william-redenbaugh/lazy-board/Housing files/Housing working/dxf 2000/Layer5.dxf

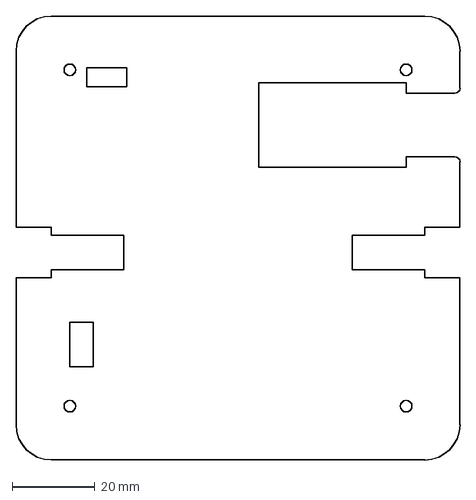
[picture p7: CAD file, 2019-08-05]
Housing files/Housing working/dxf 2000/Layer5.dxf
107.3 x 107.3 mm
