william-redenbaugh/lazy-board/lazy-code/Teensy4LazyBoard/src/led_matrix_handler.cpp

/*
Author: William Redenbaugh
Last Edit Date: 7/3/2020
*/

#include "led_matrix_handler.hpp"

// SERIAL DMA FOR LED MATRIX BEGIN // 

// default number of matrix_leds. 
const int num_matrix_led = NUM_MATRIX_LEDS;
// Default GPIO value. 
uint8_t led_matrix_gpio = LED_MATRIX_GPIO;

byte matrix_drawing_memory[num_matrix_led*3];         //  3 bytes per LED for RGB
DMAMEM byte matrix_display_memory[num_matrix_led*12]; // 12 bytes per LED for RGB

WS2812Serial matrix_leds = WS2812Serial(num_matrix_led, matrix_display_memory, matrix_drawing_memory, led_matrix_gpio, WS2812_GRB);

// SERIAL DMA FOR LED MATRIX END // 

// SERIAL DMA FOR LED UNDERGLOW BEGIN //

// Default GPIO value. 
const int num_underglow_led = UNDERGLOW_NUM_LEDS;
uint8_t led_underglow_gpio = UNDERGLOW_STRIP_GPIO;

byte underglow_drawing_memory[num_underglow_led*3];         //  3 bytes per LED for RGB
DMAMEM byte underglow_display_memory[num_underglow_led*12]; // 12 bytes per LED for RGB

WS2812Serial underglow_leds = WS2812Serial(num_underglow_led, underglow_display_memory, underglow_drawing_memory, led_underglow_gpio, WS2812_GRB);

// SERIAL DMA FOR LED UNDERGLOW END //

// Will allow us to start up our matrix from the runtime. 
extern void _start_ws2812b_matrix(void);
extern void _update_ws2812b_matrix(void);

extern void _set_ws2812b_led(uint8_t x, uint8_t y, uint8_t r, uint8_t g, uint8_t b);
extern void _set_ws2812b_macro(led_macro_t led_macro,  uint8_t r, uint8_t g, uint8_t b);

extern void _set_ws2812b_led_hsv(uint8_t x, uint8_t y, uint8_t h, uint8_t s, uint8_t v);
extern void _set_ws2812b_macro_hsv(led_macro_t led_macro, uint8_t h, uint8_t s, uint8_t v);

extern void _set_ws2812b_led_all(uint8_t r, uint8_t g, uint8_t b);
extern void _set_ws2812b_led_all_hsv(uint8_t h, uint8_t s, uint8_t v);


extern void _start_ws2812b_underglow(void);
extern void _update_ws2812b_underglow(void);

extern void _set_ws2812b_underglow_led(uint16_t led, uint8_t r, uint8_t g, uint8_t b);
extern void _set_ws2812b_underglow_led_hsv(uint16_t led, uint8_t h, uint8_t s, uint8_t v);

extern void _set_ws2812b_underglow_all(uint8_t r, uint8_t g, uint8_t b);
extern void _set_ws2812b_underglow_all_hsv(uint8_t h, uint8_t s, uint8_t v);

/**************************************************************************/
/*!
    @brief Set's up the ws2812b rgb matrix so it's ready for us to push data!
*/
/**************************************************************************/
extern void _start_ws2812b_matrix(void){
    matrix_leds.begin();
    matrix_leds.show();
}

/**************************************************************************/
/*!
    @brief LED matrix function that converts x and y corridinates into LED strip values since matrix is actually a strip
    @param uint8_t x position 
    @param uint8_t y position
    @param uint8_t red
    @param uint8_t green
    @param uint8_t blue
*/
/**************************************************************************/
extern void _set_ws2812b_led(uint8_t x, uint8_t y, uint8_t r, uint8_t g, uint8_t b){
    switch(x){
    case(LED_ROW_0):
        switch(y){
        case(LED_COL_0):
        matrix_leds.setPixelColor(0, r, g, b);
        break;
        
        case(LED_COL_1):
        matrix_leds.setPixelColor(1, r, g, b);
        break;
        
        case(LED_COL_2):
        matrix_leds.setPixelColor(2, r, g, b);
        break;
        
        case(LED_COL_3):
        matrix_leds.setPixelColor(3, r, g, b);
        break;
        
        default: 
        break;
        };
        
    break;
    
    case(LED_ROW_1):
        switch(y){
        
        case(LED_COL_2):
        matrix_leds.setPixelColor(5, r, g, b);
        break;
        
        case(LED_COL_3):
        matrix_leds.setPixelColor(4, r, g, b);
        break;
        
        default:
        break;
        };
    break;

    case(LED_ROW_2):
        switch(y){
        
        case(LED_COL_2):
        matrix_leds.setPixelColor(6, r, g, b);
        break;
        
        case(LED_COL_3):
        matrix_leds.setPixelColor(7, r, g, b);
        break;

        default: 
        break;
        };
    break;

    case(LED_ROW_3):
        switch(y){
        
        case(LED_COL_0):
        matrix_leds.setPixelColor(11, r, g, b);
        break;
        
        case(LED_COL_1):
        matrix_leds.setPixelColor(10, r, g, b);
        break;
        
        case(LED_COL_2):
        matrix_leds.setPixelColor(9, r, g, b);
        break;
        
        case(LED_COL_3):
        matrix_leds.setPixelColor(8, r, g, b);
        break;

        default: 
        break;
        };
    break;
    default:
    break;
    }
}

/**************************************************************************/
/*!
    @brief Allows us to set all of our matrix leds to a specific HSV value
    @param led_macro_t (which led are we controlling)
    @param uint8_t(red)
    @param uint8_t(green)
    @param uint8_t(blue)
*/
/**************************************************************************/
extern void _set_ws2812b_macro(led_macro_t led_macro,  uint8_t r, uint8_t g, uint8_t b){
    switch (led_macro){
    case(LED_MACRO_0_POS):
        matrix_leds.setPixelColor(0, r, g, b);
    break;
    case(LED_MACRO_1_POS):
        matrix_leds.setPixelColor(1, r, g, b);
    break;
    case(LED_MACRO_2_POS):
        matrix_leds.setPixelColor(2, r, g, b);
    break;
    case(LED_MACRO_3_POS):
        matrix_leds.setPixelColor(3, r, g, b);
    break;
    case(LED_MACRO_4_POS):
        matrix_leds.setPixelColor(5, r, g, b);
    break;
    case(LED_MACRO_5_POS):
        matrix_leds.setPixelColor(4, r, g, b);
    break;
    case(LED_MACRO_7_POS):
        matrix_leds.setPixelColor(7, r, g, b);
    break;
    case(LED_MACRO_6_POS):
        matrix_leds.setPixelColor(6, r, g, b);
    break;
    case(LED_MACRO_8_POS):
        matrix_leds.setPixelColor(11, r, g, b);
    break;
    case(LED_MACRO_9_POS):
        matrix_leds.setPixelColor(10, r, g, b);
    break;
    case(LED_MACRO_10_POS):
        matrix_leds.setPixelColor(9, r, g, b);
    break;
    case(LED_MACRO_11_POS):
        matrix_leds.setPixelColor(8, r, g, b);
    break;
    default:
    break;
    }
}

/**************************************************************************/
/*!
    @brief Allows us to set all of our matrix leds to a specific HSV value
    @param uint8_t (x position)
    @param uint8_t (y position)
    @param uint8_t(hue)
    @param uint8_t(saturation)
    @param uint8_t(value)
*/
/**************************************************************************/
extern void _set_ws2812b_led_hsv(uint8_t x, uint8_t y, uint8_t h, uint8_t s, uint8_t v){
    HsvColor hsv; 
    hsv.h = h; 
    hsv.s = s; 
    hsv.v = v; 
    RgbColor rgb = HsvToRgb(hsv);

    _set_ws2812b_led(x, y, rgb.r, rgb.g, rgb.b);
}

/**************************************************************************/
/*!
    @brief Allows us to set all of our matrix leds to a specific HSV value
    @param led_macro_t (which LED are we controlling. )
    @param uint8_t(hue)
    @param uint8_t(saturation)
    @param uint8_t(value)
*/
/**************************************************************************/
extern void _set_ws2812b_macro_hsv(led_macro_t led_macro, uint8_t h, uint8_t s, uint8_t v){
    HsvColor hsv; 
    hsv.h = h; 
    hsv.s = s; 
    hsv.v = v; 
    RgbColor rgb = HsvToRgb(hsv);

    _set_ws2812b_macro(led_macro, rgb.r, rgb.g, rgb.b);
}

/**************************************************************************/
/*!
    @brief Allows us to set all of our matrix leds to a specific HSV value
    @param uint8_t(blue)
    @param uint8_t(green)
    @param uint8_t(blue)
*/
/**************************************************************************/
extern void _set_ws2812b_led_all(uint8_t r, uint8_t g, uint8_t b){
    for(uint8_t i = 0; i < NUM_MATRIX_LEDS; i++)
        _set_ws2812b_macro((led_macro_t)i, r, g, b);
}

/**************************************************************************/
/*!
    @brief Allows us to set all of our matrix leds to a specific HSV value
    @param uint8_t(hue)
    @param uint8_t(saturation)
    @param uint8_t(value)
*/
/**************************************************************************/
extern void _set_ws2812b_led_all_hsv(uint8_t h, uint8_t s, uint8_t v){
    for(uint8_t i = 0; i < NUM_MATRIX_LEDS; i++)
        _set_ws2812b_macro_hsv((led_macro_t)i, h, s, v);
}

/**************************************************************************/
/*!
    @brief We have to update our ws2812b matrix leds
*/
/**************************************************************************/
extern void _update_ws2812b_matrix(void){
    matrix_leds.show();
}

/**************************************************************************/
/*!
    @brief Setup our underglow lighting. 
*/
/**************************************************************************/
extern void _start_ws2812b_underglow(void){
    underglow_leds.begin();
    underglow_leds.show();
}

/**************************************************************************/
/*!
    @brief We have to update our ws2812b underglow leds
*/
/**************************************************************************/
extern void _update_ws2812b_underglow(void){
    underglow_leds.show();
}

/**************************************************************************/
/*!
    @brief Allows us to set all of our underglow leds to a specific rgb value
    @param uint16_t(led) that we are controlling
    @param uint8_t(red)
    @param uint8_t(green)
    @param uint8_t(blue)
*/
/**************************************************************************/
extern void _set_ws2812b_underglow_led(uint16_t led, uint8_t r, uint8_t g, uint8_t b){
    if(led < num_underglow_led){
        underglow_leds.setPixel(led, r, g, b);
    }
}

/**************************************************************************/
/*!
    @brief Allows us to set all of our underglow leds to a specific HSV value
    @param uint16_t (led) that we are going to update
    @param uint8_t(hue)
    @param uint8_t(saturation)
    @param uint8_t(value)
*/
/**************************************************************************/
extern void _set_ws2812b_underglow_led_hsv(uint16_t led, uint8_t h, uint8_t s, uint8_t v){
    if(led < num_underglow_led){
        HsvColor hsv = {h, s, v}; 
        RgbColor rgb = HsvToRgb(hsv);
        underglow_leds.setPixel(led, rgb.r, rgb.g, rgb.b);
    }
}

/**************************************************************************/
/*!
    @brief Allows us to set all of our underglow lighting to a specific rgb value
    @param uint8_t(red)
    @param uint8_t(green)
    @param uint8_t(blue)
*/
/**************************************************************************/
extern void _set_ws2812b_underglow_all(uint8_t r, uint8_t g, uint8_t b){
    for(uint16_t i = 0; i < num_underglow_led; i++){
        underglow_leds.setPixel(i, r, g, b);
    }
}

/**************************************************************************/
/*!
    @brief Allows us to set all of our underglow leds to a specific HSV value
    @param uint8_t(hue)
    @param uint8_t(saturation)
    @param uint8_t(value)
*/
/**************************************************************************/
extern void _set_ws2812b_underglow_all_hsv(uint8_t h, uint8_t s, uint8_t v){
    HsvColor hsv = {h, s, v}; 
    RgbColor rgb = HsvToRgb(hsv);

    for(uint16_t i = 0; i < num_underglow_led; i++){
        underglow_leds.setPixel(i, rgb.r, rgb.g, rgb.b);
    }
}
