william-redenbaugh/lazy-board/lazy-code/Teensy4LazyBoard/include/spi_display_runtime.hpp

/*
Author: William Redenbaugh
Last Edit Date: 7/3/2020
*/

#ifndef _SPI_DISPLAY_RUNTIME_HPP
#define _SPI_DISPLAY_RUNTIME_HPP

// Arduino and ChibiOS Libraries 
#include "Arduino.h"
#include "ChRt.h"

#include "Adafruit_GFX.h"
#include "MessageManagement.hpp"

// LCD SPI PIN DENOMINATIONS
#define LCD_SPI_PIN_CS 10
#define LCD_SPI_PIN_MOSI 11
#define LCD_SPI_PIN_MISO 12
#define LCD_SPI_PIN_CLK 13
#define LCD_SPI_PIN_RST 8
#define LCD_SPI_PIN_DC 9

extern void start_spi_display_thread(void);
extern void trigger_new_char(char c);
extern void trigger_color(uint16_t col); 
extern void trigger_char_release(char c);
extern void process_image_flash(ImageFlash flash_config);
#endif
