william-redenbaugh/lazy-board/lazy-code/Teensy4LazyBoard/include/keyboard_runtime_thread.hpp

/*
Author: William Redenbaugh
Last Edit Date: 7/3/2020
*/

#ifndef _KEYBOARD_RUNTIME_THREAD_HPP
#define _KEYBOARD_RUNTIME_THREAD_HPP

// Arduino and ChibiOS Libraries 
#include "Arduino.h"
#include "ChRt.h"

// Keyboard gpio reading module. 
#include "keyboard_gpio.hpp"

extern void start_keyboard_runtime_thread(void); 
extern void reprogram_key(uint16_t map[], size_t map_size);

#endif 
